ScatteredDrifter/Alnitak-65/pcb/pcb.kicad_sch

## KiCad design pcb/pcb.kicad_sch (2022-04-27)

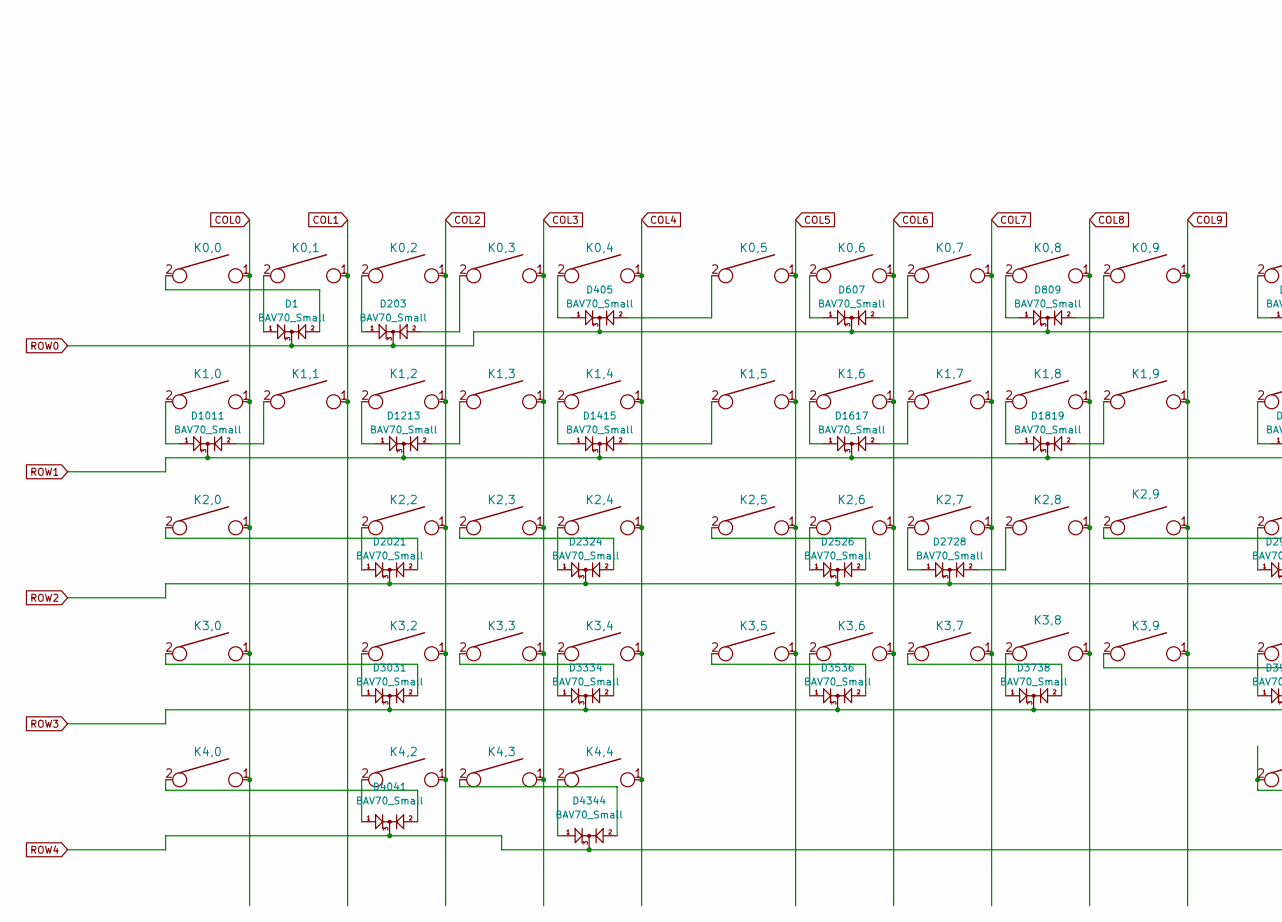
[picture p5: schematic pcb.kicad_sch, part in row 1, column 1]

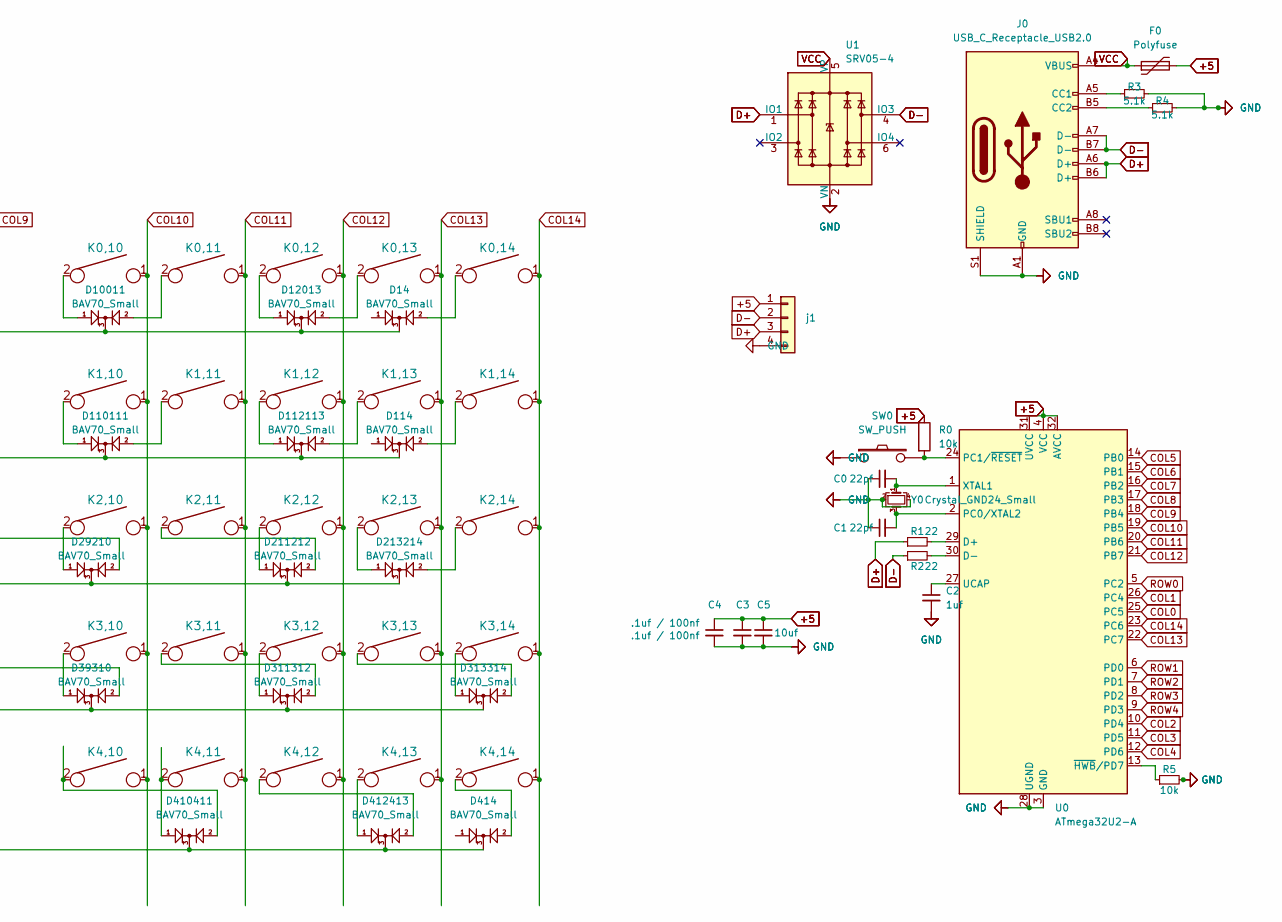
[picture p6: schematic pcb.kicad_sch, part in row 1, column 2]

Parts:
C0, C1: 22pf; C_0805_2012Metric; LCSC C1804
C2: 1uf; C_0805_2012Metric; LCSC C28323
C3, C4: .1uf / 100nf; C_0805_2012Metric; LCSC C49678
C5: 10uf; C_0805_2012Metric; LCSC C91245
D1, D14, D114, D203, D405, D414, D607, D809, D1011, D1213, D1415, D1617, D1819, D2021, D2324, D2526, D2728, D3031, D3334, D3536, D3738, D4041, D4344, D10011, D12013, D29210, D39310, D110111, D112113, D211212, D213214, D311312, D313314, D410411, D412413: BAV70_Small; SOT-23; LCSC C68978
F0: Polyfuse; Fuse_1206_3216Metric; LCSC C69688
J0: USB_C_Receptacle_USB2.0; USB_C_Receptacle_HRO_TYPE-C-31-M-12; LCSC C165948
K0,0, K0,1, K0,2, K0,3, K0,4, K0,5, K0,6, K0,7, K0,8, K0,9, K0,10, K0,11, K0,12, K0,13, K0,14, K1,0, K1,1, K1,2, K1,3, K1,4, K1,5, K1,6, K1,7, K1,8, K1,9, K1,10, K1,11, K1,12, K1,13, K1,14, K2,0, K2,2, K2,3, K2,4, K2,5, K2,6, K2,7, K2,8, K2,9, K2,10, K2,11, K2,12, K2,13, K2,14, K3,0, K3,2, K3,3, K3,4, K3,5, K3,6, K3,7, K3,8, K3,9, K3,10, K3,11, K3,12, K3,13, K3,14, K4,0, K4,2, K4,3, K4,4, K4,10, K4,11, K4,12, K4,13, K4,14: KEYSW; keyswitch_cherrymx_alps_combo_fixed
R0, R5: 10k; R_0805_2012Metric; LCSC C17414
R1, R2: 22; R_0805_2012Metric; LCSC C17561
R3, R4: 5.1k; R_0805_2012Metric; LCSC C27834
SW0: SW_PUSH; SW_SPST_TL3342; LCSC C318884
U0: ATmega32U2-A; TQFP-32_7x7mm_P0.8mm; LCSC C618733
U1: SRV05-4; SOT-23-6; LCSC C85364
Y0: Crystal_GND24_Small; Crystal_SMD_3225-4Pin_3.2x2.5mm; LCSC C13738
j1: LCSC C2845363

Connections:
+5: C3.1, C4.1, C5.1, F0.2, R0.1, U0.4 (VCC), U0.31 (UVCC), U0.32 (AVCC), j1.1
COL0: K0,0.1, K1,0.1, K2,0.1, K3,0.1, K4,0.1, U0.25 (PC5)
COL1: K0,1.1, K1,1.1, U0.26 (PC4)
COL2: K0,2.1, K1,2.1, K2,2.1, K3,2.1, K4,2.1, U0.10 (PD4)
COL3: K0,3.1, K1,3.1, K2,3.1, K3,3.1, K4,3.1, U0.11 (PD5)
COL4: K0,4.1, K1,4.1, K2,4.1, K3,4.1, K4,4.1, U0.12 (PD6)
COL5: K0,5.1, K1,5.1, K2,5.1, K3,5.1, U0.14 (PB0)
COL6: K0,6.1, K1,6.1, K2,6.1, K3,6.1, U0.15 (PB1)
COL7: K0,7.1, K1,7.1, K2,7.1, K3,7.1, U0.16 (PB2)
COL8: K0,8.1, K1,8.1, K2,8.1, K3,8.1, U0.17 (PB3)
COL9: K0,9.1, K1,9.1, K2,9.1, K3,9.1, U0.18 (PB4)
COL10: K0,10.1, K1,10.1, K2,10.1, K3,10.1, K4,10.1, U0.19 (PB5)
COL11: K0,11.1, K1,11.1, K2,11.1, K3,11.1, K4,11.1, U0.20 (PB6)
COL12: K0,12.1, K1,12.1, K2,12.1, K3,12.1, K4,12.1, U0.21 (PB7)
COL13: K0,13.1, K1,13.1, K2,13.1, K3,13.1, K4,13.1, U0.22 (PC7)
COL14: K0,14.1, K1,14.1, K2,14.1, K3,14.1, K4,14.1, U0.23 (PC6)
D+: J0.A6 (D+), J0.B6 (D+), R1.1, U1.1 (IO1), j1.3
D-: J0.A7 (D-), J0.B7 (D-), R2.1, U1.4 (IO3), j1.2
GND: C0.1, C1.1, C2.2, C3.2, C4.2, C5.2, J0.A1 (GND), J0.A12 (GND), J0.B1 (GND), J0.B12 (GND), J0.S1 (SHIELD), R3.2, R4.2, R5.2, SW0.1, U0.3 (GND), U0.28 (UGND), U1.2 (VN), Y0.2, Y0.4, j1.4
unnamed: C0.2, U0.1 (XTAL1), Y0.1
unnamed: C1.2, U0.2 (PC0/XTAL2), Y0.3
unnamed: C2.1, U0.27 (UCAP)
unnamed: D1.1 (A1), K0,1.2
unnamed: D1.2 (A2), K0,0.2
unnamed: D14.2 (A2), K0,14.2
unnamed: D114.2 (A2), K1,14.2
unnamed: D203.1 (A1), K0,2.2
unnamed: D203.2 (A2), K0,3.2
unnamed: D405.1 (A1), K0,4.2
unnamed: D405.2 (A2), K0,5.2
unnamed: D414.2 (A2), K4,14.2
unnamed: D607.1 (A1), K0,6.2
unnamed: D607.2 (A2), K0,7.2
unnamed: D809.1 (A1), K0,8.2
unnamed: D809.2 (A2), K0,9.2
unnamed: D1011.1 (A1), K1,0.2
unnamed: D1011.2 (A2), K1,1.2
unnamed: D1213.1 (A1), K1,2.2
unnamed: D1213.2 (A2), K1,3.2
unnamed: D1415.1 (A1), K1,4.2
unnamed: D1415.2 (A2), K1,5.2
unnamed: D1617.1 (A1), K1,6.2
unnamed: D1617.2 (A2), K1,7.2
unnamed: D1819.1 (A1), K1,8.2
unnamed: D1819.2 (A2), K1,9.2
unnamed: D2021.1 (A1), K2,2.2
unnamed: D2021.2 (A2), K2,0.2
unnamed: D2324.1 (A1), K2,4.2
unnamed: D2324.2 (A2), K2,3.2
unnamed: D2526.1 (A1), K2,6.2
unnamed: D2526.2 (A2), K2,5.2
unnamed: D2728.1 (A1), K2,7.2
unnamed: D2728.2 (A2), K2,8.2
unnamed: D3031.1 (A1), K3,2.2
unnamed: D3031.2 (A2), K3,0.2
unnamed: D3334.1 (A1), K3,4.2
unnamed: D3334.2 (A2), K3,3.2
unnamed: D3536.1 (A1), K3,6.2
unnamed: D3536.2 (A2), K3,5.2
unnamed: D3738.1 (A1), K3,8.2
unnamed: D3738.2 (A2), K3,7.2
unnamed: D4041.1 (A1), K4,2.2
unnamed: D4041.2 (A2), K4,0.2
unnamed: D4344.1 (A1), K4,4.2
unnamed: D4344.2 (A2), K4,3.2
unnamed: D10011.1 (A1), K0,10.2
unnamed: D10011.2 (A2), K0,11.2
unnamed: D12013.1 (A1), K0,12.2
unnamed: D12013.2 (A2), K0,13.2
unnamed: D29210.1 (A1), K2,10.2
unnamed: D29210.2 (A2), K2,9.2
unnamed: D39310.1 (A1), K3,10.2
unnamed: D39310.2 (A2), K3,9.2
unnamed: D110111.1 (A1), K1,10.2
unnamed: D110111.2 (A2), K1,11.2
unnamed: D112113.1 (A1), K1,12.2
unnamed: D112113.2 (A2), K1,13.2
unnamed: D211212.1 (A1), K2,12.2
unnamed: D211212.2 (A2), K2,11.2
unnamed: D213214.1 (A1), K2,13.2
unnamed: D213214.2 (A2), K2,14.2
unnamed: D311312.1 (A1), K3,12.2
unnamed: D311312.2 (A2), K3,11.2
unnamed: D313314.1 (A1), K3,14.2
unnamed: D313314.2 (A2), K3,13.2
unnamed: D410411.1 (A1), K4,11.2
unnamed: D410411.2 (A2), K4,10.2
unnamed: D412413.1 (A1), K4,13.2
unnamed: D412413.2 (A2), K4,12.2
unnamed: J0.A5 (CC1), R3.1
unnamed: J0.B5 (CC2), R4.1
unnamed: R0.2, SW0.2, U0.24 (PC1/~RESET)
unnamed: R1.2, U0.29 (D+)
unnamed: R2.2, U0.30 (D-)
unnamed: R5.1, U0.13 (~HWB/PD7)
ROW0: D1.3 (K), D14.3 (K), D203.3 (K), D405.3 (K), D607.3 (K), D809.3 (K), D10011.3 (K), D12013.3 (K), U0.5 (PC2)
ROW1: D114.3 (K), D1011.3 (K), D1213.3 (K), D1415.3 (K), D1617.3 (K), D1819.3 (K), D110111.3 (K), D112113.3 (K), U0.6 (PD0)
ROW2: D2021.3 (K), D2324.3 (K), D2526.3 (K), D2728.3 (K), D29210.3 (K), D211212.3 (K), D213214.3 (K), U0.7 (PD1)
ROW3: D3031.3 (K), D3334.3 (K), D3536.3 (K), D3738.3 (K), D39310.3 (K), D311312.3 (K), D313314.3 (K), U0.8 (PD2)
ROW4: D414.3 (K), D4041.3 (K), D4344.3 (K), D410411.3 (K), D412413.3 (K), U0.9 (PD3)
VCC: F0.1, J0.A4 (VBUS), J0.A9 (VBUS), J0.B4 (VBUS), J0.B9 (VBUS), U1.5 (VP)
